skhg/weather-station/testing/sds011/sds011.ino

/**
 * Copyright 2020 Jack Higgins : https://github.com/skhg
 * All components of this project are licensed under the MIT License.
 * See the LICENSE file for details.
 */

#include "SdsDustSensor.h"

int rxPin = D4;
int txPin = D3;
SdsDustSensor sds(rxPin, txPin);

void setup() {
  Serial.begin(9600);
  sds.begin();

  Serial.println(sds.queryFirmwareVersion().toString());
  Serial.println(sds.setQueryReportingMode().toString());
}

void loop() {
  sds.wakeup();
  delay(30000);  // working 30 seconds

  PmResult pm = sds.queryPm();
  if (pm.isOk()) {
    Serial.print("PM2.5 = ");
    Serial.print(pm.pm25);
    Serial.print(", PM10 = ");
    Serial.println(pm.pm10);

    Serial.println(pm.toString());
  } else {
    Serial.print("Could not read values from sensor, reason: ");
    Serial.println(pm.statusToString());
  }

  WorkingStateResult state = sds.sleep();
  if (state.isWorking()) {
    Serial.println("Problem with sleeping the sensor.");
  } else {
    Serial.println("Sensor is sleeping");
    delay(60000);  // wait 1 minute
  }
}
